steand/mGaugeESP/include/btIconOff_40x40.h

#include <Arduino.h>

#define BTICONOFF_40X40_HEIGHT 40
#define BTICONOFF_40X40_WIDTH 40

// array size is 3200
static const uint16_t btIconOff_40x40[] PROGMEM  = {
  0x0000, 0x0000, 0x0000, 0x0000, 0x0000, 0x0000, 0x0000, 0x0000, 0x0000, 0x0000, 0x0000, 0x0000, 0x2841, 0x48a2, 0x7104, 0xa186, 0xb9e7, 0xd228, 0xda49, 0xe269, 0xe269, 0xda49, 0xd228, 0xb9e7, 0xa186, 0x7104, 0x48a2, 0x2841, 0x0000, 0x0000, 0x0000, 0x0000, 0x0000, 0x0000, 0x0000, 0x0000, 0x0000, 0x0000, 0x0000, 0x0000, 
  0x0000, 0x0000, 0x0000, 0x0000, 0x0000, 0x0000, 0x0000, 0x0000, 0x0000, 0x0000, 0x2841, 0x7104, 0xa186, 0xca08, 0xe249, 0xe269, 0xe269, 0xe269, 0xe269, 0xe269, 0xe269, 0xe269, 0xe269, 0xe269, 0xe269, 0xe249, 0xca08, 0xa186, 0x7104, 0x2841, 0x0000, 0x0000, 0x0000, 0x0000, 0x0000, 0x0000, 0x0000, 0x0000, 0x0000, 0x0000, 
  0x0000, 0x0000, 0x0000, 0x0000, 0x0000, 0x0000, 0x0000, 0x0000, 0x0000, 0x6903, 0xa9c6, 0xd228, 0xe269, 0xe269, 0xe269, 0xe269, 0xe269, 0xe249, 0xe248, 0xe248, 0xe248, 0xe248, 0xe249, 0xe269, 0xe269, 0xe269, 0xe269, 0xe269, 0xd228, 0xa9c6, 0x6903, 0x0000, 0x0000, 0x0000, 0x0000, 0x0000, 0x0000, 0x0000, 0x0000, 0x0000, 
  0x0000, 0x0000, 0x0000, 0x0000, 0x0000, 0x0000, 0x0000, 0x2841, 0x9986, 0xca28, 0xe269, 0xe269, 0xe269, 0xe269, 0xe269, 0xe269, 0xda8c, 0xcad1, 0xc313, 0xbb14, 0xbb14, 0xc313, 0xcad1, 0xda8c, 0xe269, 0xe269, 0xe269, 0xe269, 0xe269, 0xe269, 0xca28, 0x9986, 0x2841, 0x0000, 0x0000, 0x0000, 0x0000, 0x0000, 0x0000, 0x0000, 
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
};
