steand/mGaugeESP/include/btIconOn_40x40.h

#include <Arduino.h>

#define BTICONON_40X40_HEIGHT 40
#define BTICONON_40X40_WIDTH 40

// array size is 3200
static const uint16_t btIconOn_40x40[] PROGMEM  = {
  0x0000, 0x0000, 0x0000, 0x0000, 0x0000, 0x0000, 0x0000, 0x0000, 0x0000, 0x0000, 0x0000, 0x0000, 0x0000, 0x0000, 0x0000, 0x0000, 0x0001, 0x0064, 0x00c7, 0x0108, 0x0108, 0x0108, 0x00e8, 0x0085, 0x0064, 0x0000, 0x0000, 0x0000, 0x0000, 0x0000, 0x0000, 0x0000, 0x0000, 0x0000, 0x0000, 0x0000, 0x0000, 0x0000, 0x0000, 0x0000, 
  0x0000, 0x0000, 0x0000, 0x0000, 0x0000, 0x0000, 0x0000, 0x0000, 0x0000, 0x0000, 0x0000, 0x0000, 0x0000, 0x0000, 0x00a6, 0x01ae, 0x0252, 0x02b4, 0x1317, 0x0b59, 0x0b59, 0x0359, 0x1359, 0x02d6, 0x02b4, 0x0210, 0x018c, 0x0043, 0x0000, 0x0000, 0x0000, 0x0000, 0x0000, 0x0000, 0x0000, 0x0000, 0x0000, 0x0000, 0x0000, 0x0000, 
  0x0000, 0x0000, 0x0000, 0x0000, 0x0000, 0x0000, 0x0000, 0x0000, 0x0000, 0x0000, 0x0000, 0x0000, 0x0064, 0x0210, 0x0317, 0x03bc, 0x041f, 0x043f, 0x043f, 0x043f, 0x043f, 0x043f, 0x043f, 0x043f, 0x043f, 0x03fe, 0x039b, 0x02f6, 0x018d, 0x0000, 0x0000, 0x0000, 0x0000, 0x0000, 0x0000, 0x0000, 0x0000, 0x0000, 0x0000, 0x0000, 
  0x0000, 0x0000, 0x0000, 0x0000, 0x0000, 0x0000, 0x0000, 0x0000, 0x0000, 0x0000, 0x0000, 0x0129, 0x02f7, 0x03dd, 0x041f, 0x041f, 0x041f, 0x041f, 0x041f, 0x041f, 0x041f, 0x041f, 0x041f, 0x041f, 0x041f, 0x041f, 0x041f, 0x041f, 0x03bc, 0x0252, 0x0043, 0x0000, 0x0000, 0x0000, 0x0000, 0x0000, 0x0000, 0x0000, 0x0000, 0x0000, 
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
};
