steand/mGaugeESP/include/fz35Off_40x40.h

#include <Arduino.h>

#define fz35OFF_40X40_HEIGHT 40
#define fz35OFF_40X40_WIDTH 40

// array size is 3200
static const uint16_t fz35Off_40x40[] PROGMEM  = {
  0x0000, 0x0000, 0x0000, 0x0000, 0x0000, 0x0000, 0x0000, 0x0000, 0x0000, 0x0000, 0x0000, 0x0000, 0x0000, 0x0000, 0x93cb, 0xa186, 0xb9e7, 0xd228, 0xda49, 0xe269, 0xe269, 0xda49, 0xd228, 0xb9e7, 0xa186, 0x93cb, 0x0000, 0x0000, 0x0000, 0x0000, 0x0000, 0x0000, 0x0000, 0x0000, 0x0000, 0x0000, 0x0000, 0x0000, 0x0000, 0x0000, 
  0x0000, 0x0000, 0x0000, 0x0000, 0x0000, 0x0000, 0x0000, 0x0000, 0x0000, 0x0000, 0x0000, 0x8b6a, 0xa186, 0xca08, 0xe249, 0xe269, 0xe269, 0xe269, 0xe269, 0xe269, 0xe269, 0xe269, 0xe269, 0xe269, 0xe269, 0xe249, 0xca08, 0xa186, 0x8b6a, 0x0000, 0x0000, 0x0000, 0x0000, 0x0000, 0x0000, 0x0000, 0x0000, 0x0000, 0x0000, 0x0000, 
  0x0000, 0x0000, 0x0000, 0x0000, 0x0000, 0x0000, 0x0000, 0x0000, 0x0000, 0x93aa, 0xa9c6, 0xd228, 0xe269, 0xe269, 0xe269, 0xe269, 0xe269, 0xe249, 0xe248, 0xe248, 0xe248, 0xe248, 0xe249, 0xe269, 0xe269, 0xe269, 0xe269, 0xe269, 0xd228, 0xa9c6, 0x93aa, 0x0000, 0x0000, 0x0000, 0x0000, 0x0000, 0x0000, 0x0000, 0x0000, 0x0000, 
  0x0000, 0x0000, 0x0000, 0x0000, 0x0000, 0x0000, 0x0000, 0x0000, 0x9986, 0xca28, 0xe269, 0xe269, 0xe269, 0xe269, 0xe269, 0xe269, 0xda8c, 0xcad1, 0xc313, 0xbb14, 0xbb14, 0xc313, 0xcad1, 0xda8c, 0xe269, 0xe269, 0xe269, 0xe269, 0xe269, 0xe269, 0xca28, 0x9986, 0x0000, 0x0000, 0x0000, 0x0000, 0x0000, 0x0000, 0x0000, 0x0000, 
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
};
