steand/mGaugeESP/include/fz35On_40x40.h

#include <Arduino.h>

#define fz35ON_40X40_HEIGHT 40
#define fz35ON_40X40_WIDTH 40

// array size is 3200
static const uint16_t fz35On_40x40[] PROGMEM  = {
  0x0000, 0x0000, 0x0000, 0x0000, 0x0000, 0x0000, 0x0000, 0x0000, 0x0000, 0x0000, 0x0000, 0x0000, 0x0000, 0x0000, 0xf7b6, 0xf7b6, 0xf796, 0xf796, 0xf796, 0xf796, 0xf796, 0xf796, 0xf796, 0xf796, 0xf7b6, 0xf7b6, 0x0000, 0x0000, 0x0000, 0x0000, 0x0000, 0x0000, 0x0000, 0x0000, 0x0000, 0x0000, 0x0000, 0x0000, 0x0000, 0x0000, 
  0x0000, 0x0000, 0x0000, 0x0000, 0x0000, 0x0000, 0x0000, 0x0000, 0x0000, 0x0000, 0x0000, 0xf797, 0xf796, 0xf796, 0xf796, 0xf796, 0xf796, 0xf796, 0xf796, 0xf796, 0xf796, 0xf796, 0xf796, 0xf796, 0xf796, 0xf796, 0xf796, 0xf796, 0xf797, 0x0000, 0x0000, 0x0000, 0x0000, 0x0000, 0x0000, 0x0000, 0x0000, 0x0000, 0x0000, 0x0000, 
  0x0000, 0x0000, 0x0000, 0x0000, 0x0000, 0x0000, 0x0000, 0x0000, 0x0000, 0xffd6, 0xf7b6, 0xf796, 0xf796, 0xf796, 0xf796, 0xf796, 0xf796, 0xf796, 0xf796, 0xf796, 0xf796, 0xf796, 0xf796, 0xf796, 0xf796, 0xf796, 0xf796, 0xf796, 0xf796, 0xf7b6, 0xffd6, 0x0000, 0x0000, 0x0000, 0x0000, 0x0000, 0x0000, 0x0000, 0x0000, 0x0000, 
  0x0000, 0x0000, 0x0000, 0x0000, 0x0000, 0x0000, 0x0000, 0x0000, 0xf7b6, 0xf796, 0xf796, 0xf796, 0xf796, 0xf796, 0xf796, 0xf796, 0xf796, 0xf796, 0xf796, 0xf796, 0xf796, 0xf796, 0xf796, 0xf796, 0xf796, 0xf796, 0xf796, 0xf796, 0xf796, 0xf796, 0xf796, 0xf7b6, 0x0000, 0x0000, 0x0000, 0x0000, 0x0000, 0x0000, 0x0000, 0x0000, 
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
};
