steand/mGaugeESP/src/Display.cpp

/*
   Copyright (C) 2026  by Stefan Andres (develop@andres-stefan.de)

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
   You should have received a copy of the GNU General Public License
   along with this program.  If not, see <https://www.gnu.org/licenses/>.
 */


#include "Display.h"

#include "btIconOn_40x40.h"
#include "btIconOff_40x40.h"
#include "fz35On_40x40.h"
#include "fz35Off_40x40.h"
#include "warningRed_24x24.h"
#include "warningYellow_24x24.h"

GDisplay::GDisplay()
{
  // this->tft = tft;
}

void GDisplay::begin()
{   
    _logd("Display Begin");
    tft.init();
    tft.setRotation(3);
    ina219isConneced = false;
    fz35isConneced = false;
    clear();
    _logd("Display End Begin");
}

void GDisplay::drawFrame(int x, int y)
{


  int x1=x+5;
  int x2=x+235;
  int xm=x+120;
  tft.drawLine(x1,15,x2,15,TFT_WHITE);    //Horizontal
                                          // voltage
  tft.drawLine(x1,100,x2,100,TFT_WHITE);  //Horizontal
                                          //current
  tft.drawLine(x1,185,x2,185,TFT_WHITE);  //Horizontal 
                                          // Power
  tft.drawLine(x1,270,x2,270,TFT_WHITE);  //Horizontal 

  tft.drawLine(x1,15,x1,270,TFT_WHITE);    //Vertikal
  tft.drawLine(x2,15,x2,270,TFT_WHITE);    //Vertikal

  

}

void GDisplay::drawchannel(int x, int y,String name) 
{

  drawFrame(x,y);

  tft.setTextColor(TFT_YELLOW,TFT_BLACK, true);

  tft.setTextDatum(CC_DATUM);
  tft.drawString(" "+name+" ",x+120,y+15,2);

  tft.setTextDatum(BR_DATUM);
 
  tft.drawString("V",x+215,y+90,4);

  tft.setTextColor(TFT_SKYBLUE,TFT_BLACK, true);
 
  tft.drawString("A",x+215,y+175,4);

  tft.setTextColor(TFT_GREEN,TFT_BLACK, true);
 
  tft.drawString("W",x+218,y+260,4);
 


}

void GDisplay::printValue(int x, int y, float value, int font)
{
  int w;
  if (font == 7) w = 175;
  else w = 85;
    
  tft.setTextPadding(w);
  String str = String(value,3);
  tft.setTextDatum(BR_DATUM);
  tft.drawString(str,x+w,y,font);
  
}


void GDisplay::clear()
{
  tft.fillScreen(TFT_BLACK);
  tft.setSwapBytes(true);
 
  drawchannel(0,0,"channel 0");
  drawchannel(240,0,"channel I");

  tft.setTextDatum(CL_DATUM);
  tft.setTextColor(TFT_YELLOW,TFT_BLACK, true);
  tft.drawString("out of range",230,300,2);
  tft.pushImage(200,290,24,24,warningYellow_24x24);

  tft.setTextColor(TFT_RED,TFT_BLACK, true);
  tft.drawString("overflow",360,300,2);
  tft.pushImage(330,290,24,24,warningRed_24x24);

  fz35Connected(fz35isConneced);
  btConnected(ina219isConneced);
  
}

void GDisplay::updateVoltage(int channel, float voltage, bool overload)
{
  int x;

  x = 0;
  if (channel == 1)
    x = 240;

  tft.setTextColor(TFT_YELLOW, TFT_BLACK, true);

  printValue(x + 15, 85, voltage, 7);
  
  if (overload)
  {
    tft.pushImage(x + 200, 23, 24, 24, warningYellow_24x24);
  }
  else
  {
    tft.fillRect(x + 200, 23, 24, 24,TFT_BLACK);
  }
}

void GDisplay::updateCurrent(int channel, float current, bool overload)
{

  int x;

  x = 0;
  if (channel == 1)
    x = 240;

  tft.setTextColor(TFT_SKYBLUE, TFT_BLACK, true);
  printValue(x + 15, 170, current, 7);

  if (overload)
  {
   tft.pushImage(x + 200, 108, 24, 24, warningRed_24x24);
  }
  else
  {
    tft.fillRect(x + 200, 108, 24, 24,TFT_BLACK);
    
  }
}



void GDisplay::updatePower(int channel, float power, bool overload)
{
  int x;

  x = 0;
  if (channel == 1)
    x = 240;

  tft.setTextColor(TFT_GREEN, TFT_BLACK, true);

  printValue(x + 15, 255, power, 7);
  if (overload)
  {
   tft.pushImage(x + 200, 193, 24, 24, warningYellow_24x24);
  }
  else
  {
    tft.fillRect(x + 200, 108, 24, 24,TFT_BLACK);
    
  }

}

void GDisplay::drawSetup()
{
  tft.fillScreen(TFT_BLACK);
  tft.setTextColor(TFT_WHITE, TFT_BLACK, true);
  tft.setTextDatum(BL_DATUM);
  tft.drawString("Setup INA219 Resistors",5,30,4);
  tft.drawString("Channel 0:",20,70,4);
  tft.drawString("Channel 1:",20,120,4);
  tft.drawString("Save",20,170,4);
  tft.drawString("Exit",20,220,4);
}

void GDisplay::drawSetupResistor(uint8_t channel, float resistor, float current, boolean active)
{
  String s;
  int y = 70;
  if (channel == 1 ) y = 120;
  tft.setTextPadding(100);
  tft.setTextDatum(BR_DATUM);
  if (active) tft.setTextColor(TFT_YELLOW, TFT_BLACK, true);
  s=String(resistor,3)+"Ohm";
  tft.drawString(s,280,y,4);
  tft.setTextColor(TFT_WHITE, TFT_BLACK, true);
  s=String(current,3)+"A";
  tft.drawString(s,410,y,4);

}

void GDisplay::activatePos(uint8_t pos)
{
  int32_t x1,x2,x3,y1,y2,y3;
  const uint8_t posd[] ={60,110,160,210};

  tft.fillTriangle(5,posd[lastPos],5,posd[lastPos]-20,15,posd[lastPos]-10, TFT_BLACK);
  tft.fillTriangle(5,posd[pos],5,posd[pos]-20,15,posd[pos]-10, TFT_ORANGE);
  lastPos = pos;
}

void GDisplay::btConnected(boolean connect)
{
  if (connect) {
    fz35isConneced = true;
    tft.pushImage(20,280,40,40,btIconOn_40x40);
  } else {
    fz35isConneced = false;
    tft.pushImage(20,280,40,40,btIconOff_40x40);
  }
}

void GDisplay::fz35Connected(boolean connect)
{
  if (connect) {
    ina219isConneced = true;
    tft.pushImage(80,280,40,40,fz35On_40x40);
  } else {
    ina219isConneced = false;
    tft.pushImage(80,280,40,40,fz35Off_40x40);
  }
}
