steand/mGaugeESP/include/warningYellow_24x24.h

#include <Arduino.h>

#define WARNINGYELLOW_24X24_HEIGHT 24
#define WARNINGYELLOW_24X24_WIDTH 24

// array size is 1152
static const uint16_t warningYellow_24x24[] PROGMEM  = {
  0x0000, 0x0000, 0x0000, 0x0000, 0x0000, 0x0000, 0x0000, 0x0000, 0x0000, 0x0000, 0xc600, 0xd6a0, 0xd6a0, 0xc600, 0x0000, 0x0000, 0x0000, 0x0000, 0x0000, 0x0000, 0x0000, 0x0000, 0x0000, 0x0000, 
  0x0000, 0x0000, 0x0000, 0x0000, 0x0000, 0x0000, 0x0000, 0x0000, 0x0000, 0xce63, 0xe720, 0xffe0, 0xffe0, 0xe720, 0xce63, 0x0000, 0x0000, 0x0000, 0x0000, 0x0000, 0x0000, 0x0000, 0x0000, 0x0000, 
  0x0000, 0x0000, 0x0000, 0x0000, 0x0000, 0x0000, 0x0000, 0x0000, 0x0000, 0xce40, 0xffe0, 0xffe0, 0xffe0, 0xffe0, 0xce40, 0x0000, 0x0000, 0x0000, 0x0000, 0x0000, 0x0000, 0x0000, 0x0000, 0x0000, 
  0x0000, 0x0000, 0x0000, 0x0000, 0x0000, 0x0000, 0x0000, 0x0000, 0xc600, 0xe720, 0xffe0, 0xffe0, 0xffe0, 0xffe0, 0xe720, 0xce63, 0x0000, 0x0000, 0x0000, 0x0000, 0x0000, 0x0000, 0x0000, 0x0000, 
  0x0000, 0x0000, 0x0000, 0x0000, 0x0000, 0x0000, 0x0000, 0x0000, 0xd6a0, 0xffe0, 0xffe0, 0xffe0, 0xffe0, 0xffe0, 0xffe0, 0xce40, 0x0000, 0x0000, 0x0000, 0x0000, 0x0000, 0x0000, 0x0000, 0x0000, 
  0x0000, 0x0000, 0x0000, 0x0000, 0x0000, 0x0000, 0x0000, 0xbdc0, 0xffc0, 0xffe0, 0xffe0, 0xffe0, 0xffe0, 0xffe0, 0xffe0, 0xe720, 0xce63, 0x0000, 0x0000, 0x0000, 0x0000, 0x0000, 0x0000, 0x0000, 
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
  0x0000, 0xc600, 0xd6a0, 0xd6a0, 0xd6a0, 0xd6a0, 0xd6a0, 0xd6a0, 0xd6a0, 0xd6a0, 0xd6a0, 0xd6a0, 0xd6a0, 0xd680, 0xd6a0, 0xd6a0, 0xd6a0, 0xd6a0, 0xd6a0, 0xd6a0, 0xd6a0, 0xd6a0, 0xc600, 0x0000
};
