steand/mGaugeESP/include/warningIcon.h

#include <Arduino.h>

#define WARNINGICON_HEIGHT 24
#define WARNINGICON_WIDTH 24

// array size is 1152
static const uint16_t warningIcon[] PROGMEM  = {
  0x0000, 0x0000, 0x0000, 0x0000, 0x0000, 0x0000, 0x0000, 0x0000, 0x0000, 0xfd4f, 0xf32a, 0xfb8c, 0xfb8b, 0xfb8b, 0xfccc, 0x0000, 0x0000, 0x0000, 0x0000, 0x0000, 0x0000, 0x0000, 0x0000, 0x0000, 
  0x0000, 0x0000, 0x0000, 0x0000, 0x0000, 0x0000, 0x0000, 0x0000, 0xffff, 0xfbac, 0xfc2f, 0xfdb5, 0xfd95, 0xfc0e, 0xfb6b, 0xffff, 0x0000, 0x0000, 0x0000, 0x0000, 0x0000, 0x0000, 0x0000, 0x0000, 
  0x0000, 0x0000, 0x0000, 0x0000, 0x0000, 0x0000, 0x0000, 0x0000, 0xfcf2, 0xfb6c, 0xf5b6, 0xfc0e, 0xfc2f, 0xfdb5, 0xfb8c, 0xfcaf, 0x0000, 0x0000, 0x0000, 0x0000, 0x0000, 0x0000, 0x0000, 0x0000, 
  0x0000, 0x0000, 0x0000, 0x0000, 0x0000, 0x0000, 0x0000, 0x0000, 0xfb4a, 0xfcb1, 0xfd33, 0xf9a0, 0xf9c1, 0xfd54, 0xfc70, 0xf34b, 0x0000, 0x0000, 0x0000, 0x0000, 0x0000, 0x0000, 0x0000, 0x0000, 
  0x0000, 0x0000, 0x0000, 0x0000, 0x0000, 0x0000, 0x0000, 0xf3ed, 0xfae9, 0xfe38, 0xfac8, 0xf9a0, 0xf9a0, 0xfb0a, 0xf638, 0xfac8, 0xf46f, 0x0000, 0x0000, 0x0000, 0x0000, 0x0000, 0x0000, 0x0000, 
  0x0000, 0x0000, 0x0000, 0x0000, 0x0000, 0x0000, 0xfeb5, 0xfac8, 0xf575, 0xfcd1, 0xf960, 0xf9a0, 0xf9a0, 0xf960, 0xfd13, 0xfd54, 0xfaa8, 0xfdf7, 0x0000, 0x0000, 0x0000, 0x0000, 0x0000, 0x0000, 
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
  0xfbef, 0xf2ca, 0xf2eb, 0xf32c, 0xf30c, 0xf30c, 0xf30c, 0xf30c, 0xf30c, 0xf30c, 0xf30c, 0xf30c, 0xf30c, 0xf30c, 0xf30c, 0xf30c, 0xf30c, 0xf30c, 0xf30c, 0xf30c, 0xf32c, 0xfacb, 0xf2ca, 0xfc92
};
